foldvarid93/Wooden_LED_MatrixClock/03_Software/01_Wooden_LED_MatrixClock_TrueStudio/Inc/main.h

#define USART2_TX_Pin GPIO_PIN_2
#define USART2_TX_GPIO_Port GPIOA
#define USART2_RX_Pin GPIO_PIN_3
#define USART2_RX_GPIO_Port GPIOA
#define LS_ADC1_IN4_Pin GPIO_PIN_4
#define LS_ADC1_IN4_GPIO_Port GPIOA
#define SPI2_CS_Pin GPIO_PIN_12
#define SPI2_CS_GPIO_Port GPIOB
#define SWDIO_Pin GPIO_PIN_13
#define SWDIO_GPIO_Port GPIOA
#define SWDCLK_Pin GPIO_PIN_14
#define SWDCLK_GPIO_Port GPIOA
#define ESP8266_RST_Pin GPIO_PIN_8
#define ESP8266_RST_GPIO_Port GPIOB
#define ESP8266_EN_Pin GPIO_PIN_9
#define ESP8266_EN_GPIO_Port GPIOB
