foldvarid93/Wooden_LED_MatrixClock/03_Software/02_Wooden_LED_MatrixClock_CubeIDE/Src/characters.c

#include "characters.h"
const uint8_t characters[256][6] ={
	{0xFF,0xFF,0xFF,0xFF,0xFF,0xFF},//0	
	{0xFF,0xFF,0xFF,0xFF,0xFF,0xFF},//1
	{0xFF,0xFF,0xFF,0xFF,0xFF,0xFF},//2
	{0xFF,0xFF,0xFF,0xFF,0xFF,0xFF},//3
	{0xFF,0xFF,0xFF,0xFF,0xFF,0xFF},//4
	{0xFF,0xFF,0xFF,0xFF,0xFF,0xFF},//5
	{0xFF,0xFF,0xFF,0xFF,0xFF,0xFF},//6
	{0xFF,0xFF,0xFF,0xFF,0xFF,0xFF},//7
	{0xFF,0xFF,0xFF,0xFF,0xFF,0xFF},//8
	{0xFF,0xFF,0xFF,0xFF,0xFF,0xFF},//9
	{0xFF,0xFF,0xFF,0xFF,0xFF,0xFF},// A
	{0xFF,0xFF,0xFF,0xFF,0xFF,0xff},//B
	{0xFF,0xFF,0xFF,0xFF,0xFF,0xFF},//C
	{0xFF,0xFF,0xFF,0xFF,0xFF,0xFF},//D
	{0xFF,0xFF,0xFF,0xFF,0xFF,0xff},//E
	{0xFF,0xFF,0xFF,0xFF,0xFF,0xff},//F
	{0xFF,0xFF,0xFF,0xFF,0xFF,0xff},//10
	{0xFF,0xFF,0xFF,0xFF,0xFF,0xff},//11
	{0xFF,0xFF,0xFF,0xFF,0xFF,0xff},//12
	{0xFF,0xFF,0xFF,0xFF,0xFF,0xFF},//13
	{0xFF,0xFF,0xFF,0xFF,0xFF,0xFF},//14
	{0xFF,0xFF,0xFF,0xFF,0xFF,0xFF},//15
	{0xFF,0xFF,0xFF,0xFF,0xFF,0xFF},//16
	{0xFF,0xFF,0xFF,0xFF,0xFF,0xFF},//17
	{0xFF,0xFF,0xFF,0xFF,0xFF,0xFF},//18
	{0xFF,0xFF,0xFF,0xFF,0xFF,0xFF},//19
	{0xFF,0xFF,0xFF,0xFF,0xFF,0xFF},//1A
	{0xFF,0xFF,0xFF,0xFF,0xFF,0xFF},//1B
	{0xFF,0xFF,0xFF,0xFF,0xFF,0xFF},//1C
	{0xFF,0xFF,0xFF,0xFF,0xFF,0xFF},//1D
	{0xFF,0xFF,0xFF,0xFF,0xFF,0xFF},//1E
	{0xFF,0xFF,0xFF,0xFF,0xFF,0xFF},//1F
	{0xFF,0xFF,0xFF,0xFF,0xFF,0xFF},//space	20H
	{0xFF,0xFF,0x41,0xFF,0xFF,0xFF},//!	21H
	{0xFF,0xF8,0xFF,0xF8,0xFF,0xFF},//"	22H
	{0xD7,0x01,0xD7,0x01,0xD7,0xFF},//#	23H
	{0xB7,0xAB,0x01,0xAB,0xDB,0xFF},//$	24H
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
	{0xFF,0xFF,0xFF,0xFF,0xFF,0xFF},//F9H
	{0x87,0x7F,0x7C,0xBF,0x07,0xFF},
	{0x87,0x7C,0x7F,0xBC,0x07,0xFF},
	{0x87,0x7D,0x7F,0xBD,0x07,0xFF},
	{0xFF,0xFF,0xFF,0xFF,0xFF,0xFF},//FDH
	{0xFF,0xFF,0xFF,0xFF,0xFF,0xFF},//FEH
	{0xFF,0xFF,0xFF,0xFF,0xFF,0xFF}//FFH		
};	
