foldvarid93/Wooden_LED_MatrixClock/03_Software/01_Wooden_LED_MatrixClock_TrueStudio/Src/esp8266_webpage.c

#include "main.h"

uint8_t webpage[1271];
void InitWebpage(){
	webpage[0]='<';
	webpage[1]='!';
	webpage[2]='D';
	webpage[3]='O';
	webpage[4]='C';
	webpage[5]='T';
	webpage[6]='Y';
	webpage[7]='P';
	webpage[8]='E';
	webpage[9]=' ';
	webpage[10]='h';
	webpage[11]='t';
	webpage[12]='m';
	webpage[13]='l';
	webpage[14]='>';
	webpage[15]='\n';
	webpage[16]='<';
	webpage[17]='h';
	webpage[18]='t';
	webpage[19]='m';
	webpage[20]='l';
	webpage[21]='>';
	webpage[22]='\n';
	webpage[23]='<';
	webpage[24]='h';
	webpage[25]='e';
	webpage[26]='a';
	webpage[27]='d';
	webpage[28]='>';
	webpage[29]='\n';
	webpage[30]='<';
	webpage[31]='t';
	webpage[32]='i';
	webpage[33]='t';
	webpage[34]='l';
	webpage[35]='e';
	webpage[36]='>';
	webpage[37]='e';
	webpage[38]='s';
	webpage[39]='p';
	webpage[40]='8';
	webpage[41]='2';
	webpage[42]='6';
	webpage[43]='6';
	webpage[44]=' ';
	webpage[45]='t';
	webpage[46]='e';
	webpage[47]='s';
	webpage[48]='t';
	webpage[49]=' ';
	webpage[50]='p';
	webpage[51]='a';
	webpage[52]='g';
	webpage[53]='e';
	webpage[54]='<';
	webpage[55]='/';
	webpage[56]='t';
	webpage[57]='i';
	webpage[58]='t';
	webpage[59]='l';
	webpage[60]='e';
	webpage[61]='>';
	webpage[62]='\n';
	webpage[63]='<';
	webpage[64]='/';
	webpage[65]='h';
	webpage[66]='e';
	webpage[67]='a';
	webpage[68]='d';
	webpage[69]='>';
	webpage[70]='\n';
	webpage[71]='<';
	webpage[72]='b';
	webpage[73]='o';
	webpage[74]='d';
	webpage[75]='y';
	webpage[76]='>';
	webpage[77]='\n';
	webpage[78]='<';
	webpage[79]='h';
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
	webpage[1232]='(';
	webpage[1233]='n';
	webpage[1234]='u';
	webpage[1235]='l';
	webpage[1236]='l';
	webpage[1237]=')';
	webpage[1238]=';';
	webpage[1239]='\n';
	webpage[1240]='}';
	webpage[1241]='\n';
	webpage[1242]='<';
	webpage[1243]='/';
	webpage[1244]='s';
	webpage[1245]='c';
	webpage[1246]='r';
	webpage[1247]='i';
	webpage[1248]='p';
	webpage[1249]='t';
	webpage[1250]='>';
	webpage[1251]='\n';
	webpage[1252]='<';
	webpage[1253]='/';
	webpage[1254]='b';
	webpage[1255]='o';
	webpage[1256]='d';
	webpage[1257]='y';
	webpage[1258]='>';
	webpage[1259]='\n';
	webpage[1260]='\n';
	webpage[1261]='<';
	webpage[1262]='/';
	webpage[1263]='h';
	webpage[1264]='t';
	webpage[1265]='m';
	webpage[1266]='l';
	webpage[1267]='>';
	webpage[1268]='\r';
	webpage[1269]='\n';
	webpage[1270]='\0';
}
