foldvarid93/Wooden_LED_MatrixClock/03_Software/02_Wooden_LED_MatrixClock_CubeIDE/Inc/esp8266.h

#ifndef __ESP8266_H
#define __ESP8266_H
/***************************************************************************************
 * Includes
 **************************************************************************************/
#include "typedef.h"
#include "application.h"
/***************************************************************************************
 * Defines
 **************************************************************************************/
#define SizeOf_HTML_Message		(2048u)
/**/
#define AT_OK					"OK"
#define AT_READY				"ready"
#define HTML_OK					"HTTP/1.1 200 OK\r\nContent-Type: text/html\r\nConnection: close\r\n\r\n"
/*group 0*/
#define MSG_ID00_START			"MsG_STRT-iD_00"
#define MSG_ID00_STOP			"MsG_STOP-iD_00"
#define MSG_ID01_START			"MsG_STRT-iD_01"
#define MSG_ID01_STOP			"MsG_STOP-iD_01"
#define MSG_ID02_START			"MsG_STRT-iD_02"
#define MSG_ID02_STOP			"MsG_STOP-iD_02"
#define MSG_ID03_START			"MsG_STRT-iD_03"
#define MSG_ID03_STOP			"MsG_STOP-iD_03"
#define MSG_ID04_START			"MsG_STRT-iD_04"
#define MSG_ID04_STOP			"MsG_STOP-iD_04"
#define MSG_ID05_START			"MsG_STRT-iD_05"
#define MSG_ID05_STOP			"MsG_STOP-iD_05"
#define MSG_ID06_START			"MsG_STRT-iD_06"
#define MSG_ID06_STOP			"MsG_STOP-iD_06"
#define MSG_ID07_START			"MsG_STRT-iD_07"
#define MSG_ID07_STOP			"MsG_STOP-iD_07"
#define MSG_ID08_START			"MsG_STRT-iD_08"
#define MSG_ID08_STOP			"MsG_STOP-iD_08"
#define MSG_ID09_START			"MsG_STRT-iD_09"
#define MSG_ID09_STOP			"MsG_STOP-iD_09"
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
/**/
HAL_StatusTypeDef ESP8266_AccessPoint_InitAndRun(void);
/**/
HAL_StatusTypeDef HTML_GetMessage(uint8_t * Message);
/**/
HAL_StatusTypeDef HTML_Interpreter(uint8_t * Message);
/**/
/**************************************************************************************/
#endif
