foldvarid93/Wooden_LED_MatrixClock/03_Software/02_Wooden_LED_MatrixClock_CubeIDE/Inc/tmp100.h

/*
 * tmp100.h
 *
 *  Created on: 2020. okt. 23.
 *      Author: David
 */

#ifndef TMP100_H_
#define TMP100_H_
/**** INCLUDES ***********************************************************************************/
#include "i2c.h"
#include "typedef.h"
/**** END OF INCLUDES ****************************************************************************/

/**** MACROS *************************************************************************************/
#define TMP100_ADDR  	(0x48 << 1) // Use 8-bit address
#define REG_TEMP  		(0x00)
/**** END OF MACROS ******************************************************************************/

/**** TYPE DEFINITIONS ***************************************************************************/

/**** END OF TYPE DEFINITIONS ********************************************************************/

/**** VARIABLES **********************************************************************************/

/**** END OF VARIABLES ***************************************************************************/

/**** LOCAL FUNCTION DECLARATIONS ****************************************************************/
HAL_StatusTypeDef TMP100_GetTemp(float* Temperature);
/**** END OF LOCAL FUNCTION DECLARATIONS *********************************************************/

/**** LOCAL FUNCTION DEFINITIONS *****************************************************************/

/**** END OF LOCAL FUNCTION DEFINITIONS **********************************************************/

/**** GLOBAL FUNCTION DEFINITIONS ****************************************************************/

/**** END OF GLOBAL FUNCTION DEFINITIONS *********************************************************/

#endif /* TMP100_H_ */
